advaitconty/Modulus/Readme Images/Screenshot from 2026-03-16 23-16-39.png

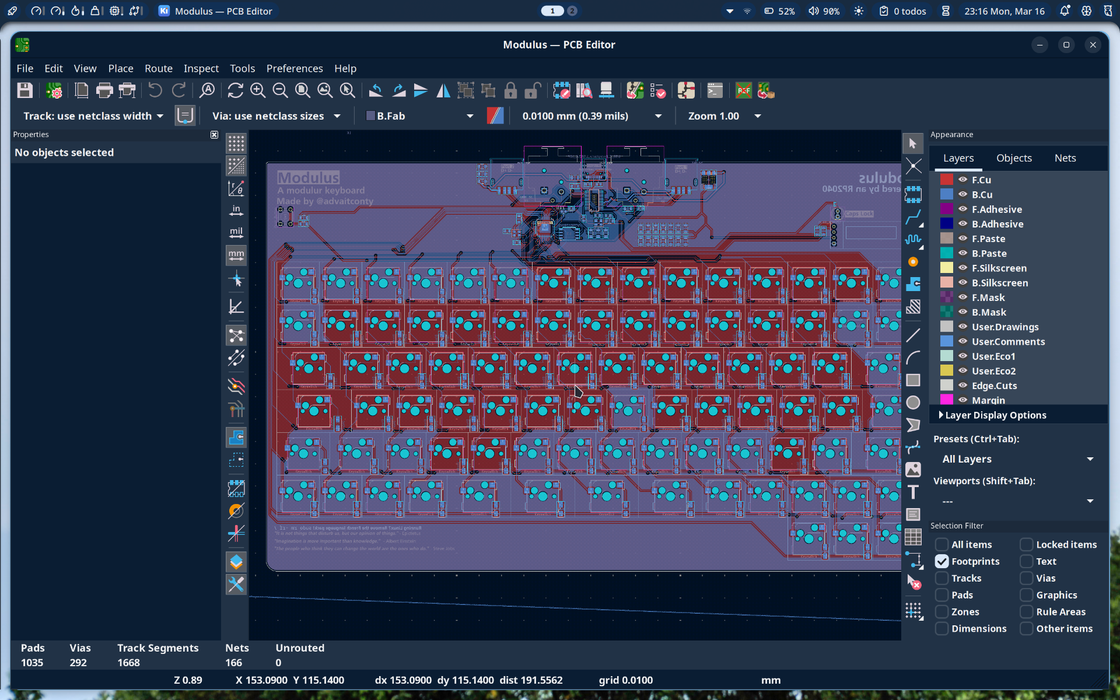
Readme Images/Screenshot from 2026-03-16 23-16-39.png
